FJLabs-Designs/FJ60BLX/Renders/v1-7-17-20-top.JPEG

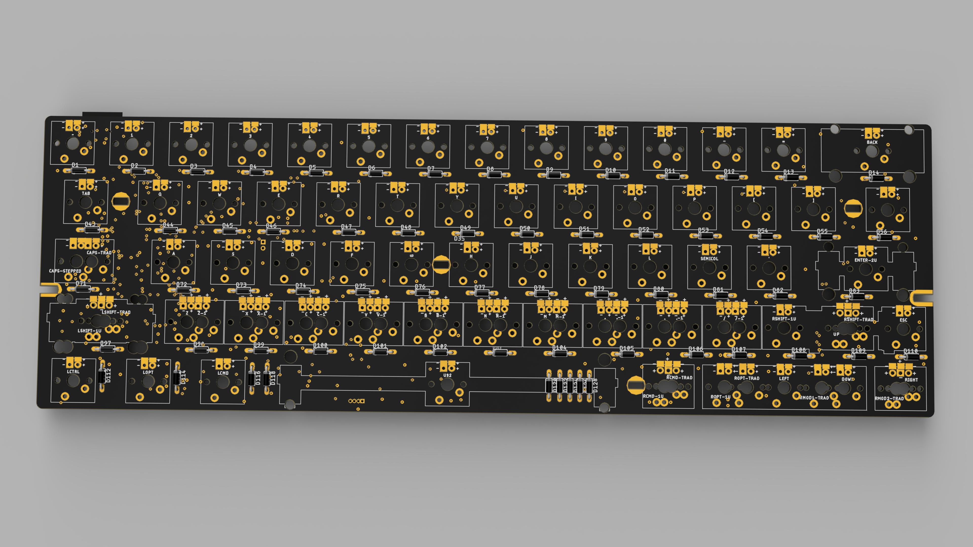
Renders/v1-7-17-20-top.JPEG
