FJLabs-Designs/FJ60BLX/Renders/v1-7-19-20-Bottom-2.jpg

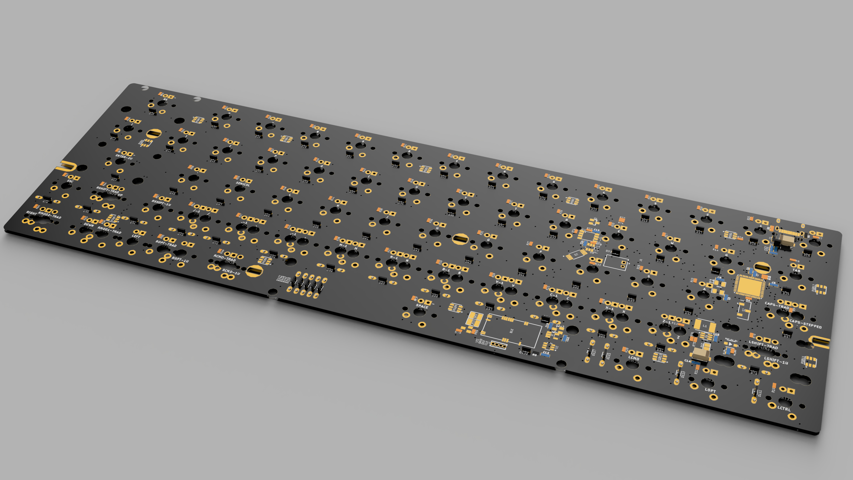
Renders/v1-7-19-20-Bottom-2.jpg
