FJLabs-Designs/FJ60BLX/Renders/v1-7-19-20-Top.jpg

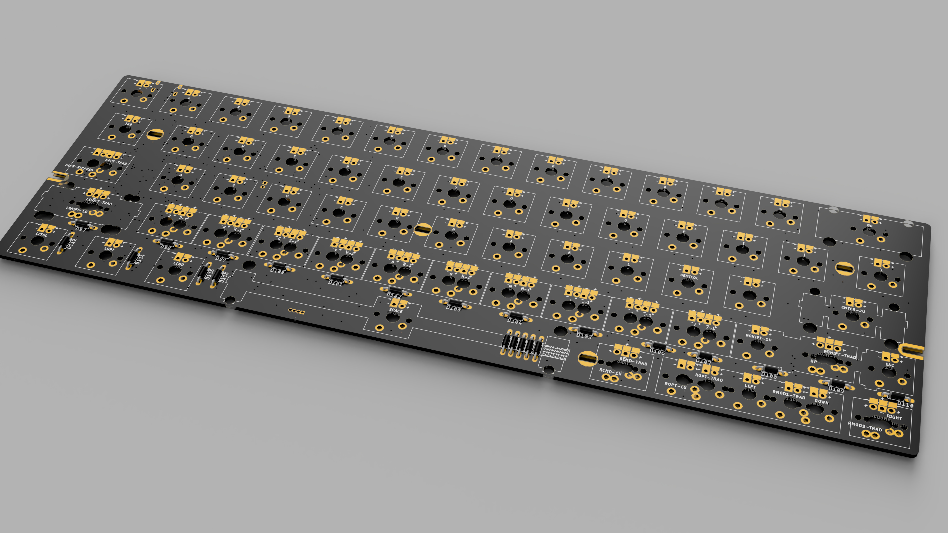
Renders/v1-7-19-20-Top.jpg
