FJLabs-Designs/FJ60BLX/Renders/v1-7-26-20-Split_Backspace.jpg

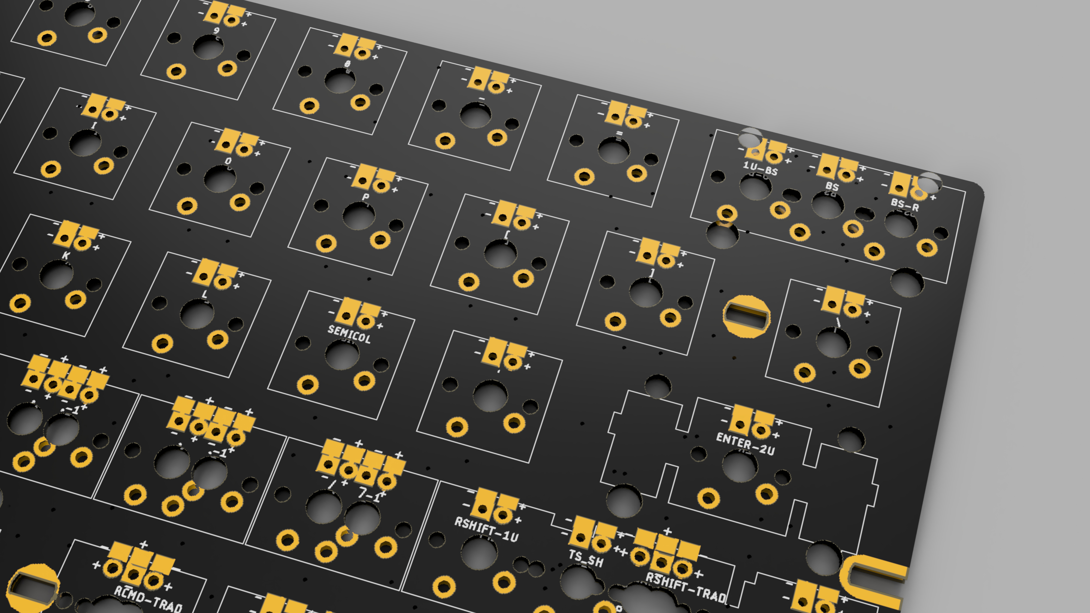
Renders/v1-7-26-20-Split_Backspace.jpg
