FJLabs-Designs/FJ60BLX/Renders/v1-7-26-20-TS_RShift.jpg

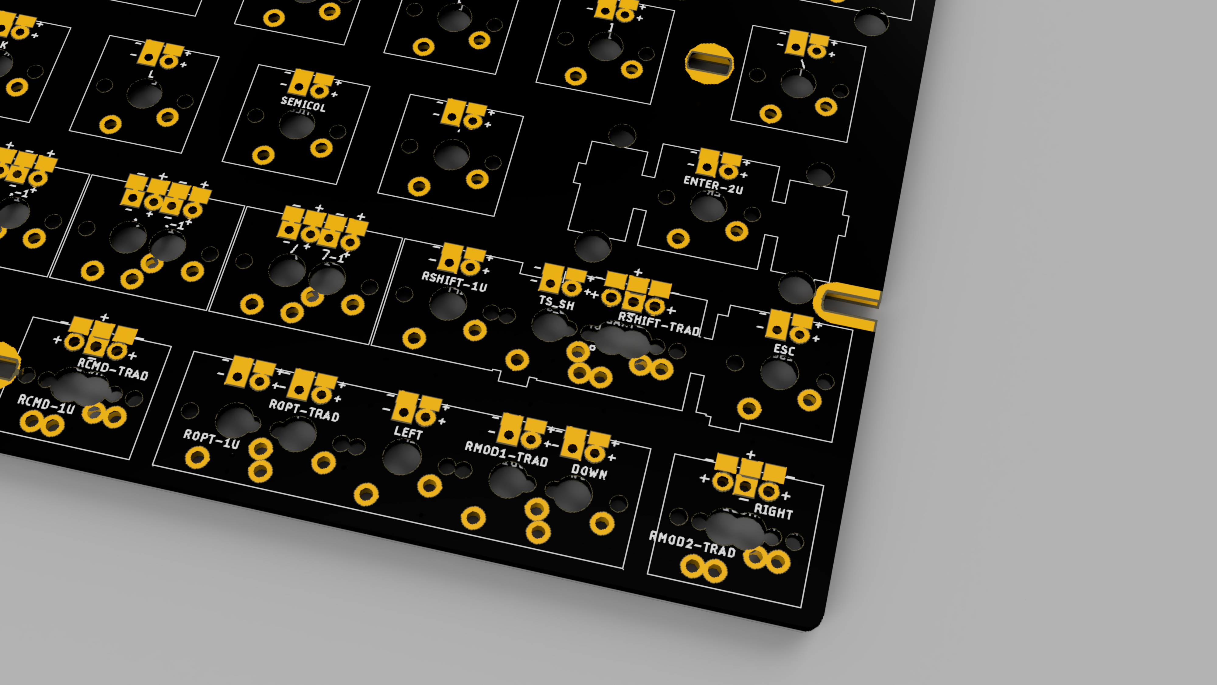
Renders/v1-7-26-20-TS_RShift.jpg
