FJLabs-Designs/FJ60BLX/Renders/v1-08-05-20-bottom.jpg

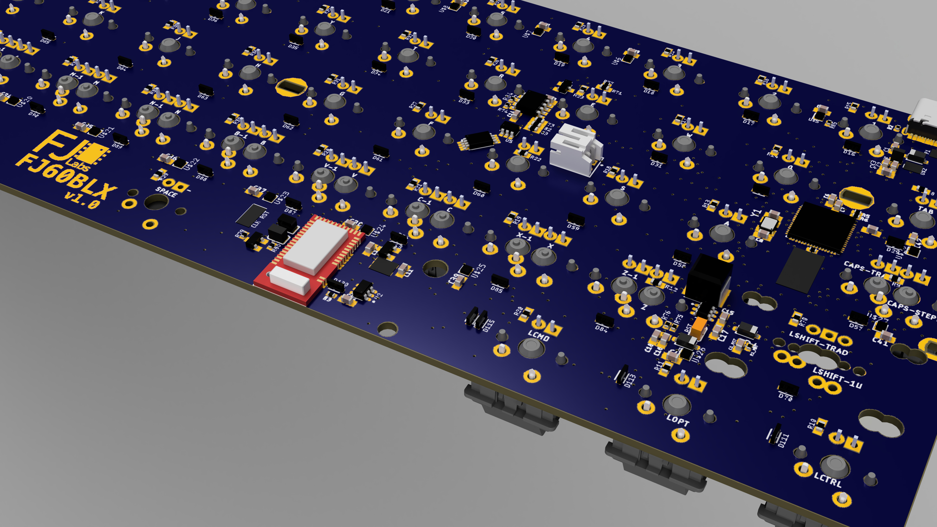
Renders/v1-08-05-20-bottom.jpg
