FJLabs-Designs/FJ60BLX/Renders/v1-8-20-20-whole.png

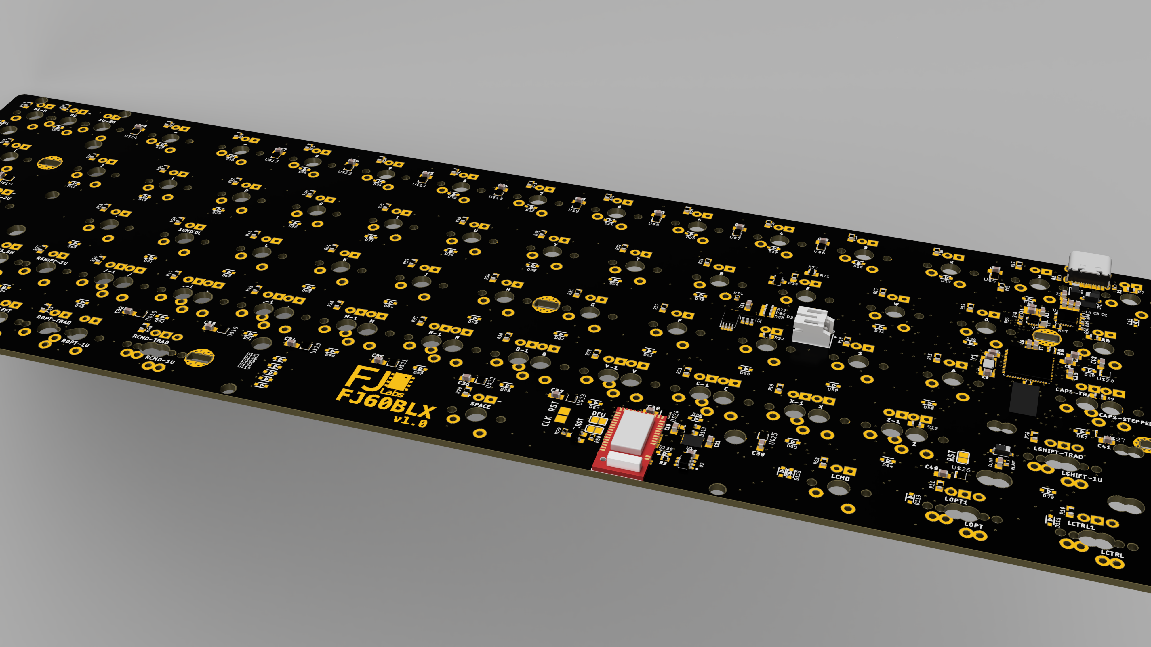
Renders/v1-8-20-20-whole.png
