FJLabs-Designs/FJ60BLX/Bill of Materials/GitHub BOM 9-4-2020.xlsx

Qty | Value | Device | Package | Parts | Description | Technology | Manufacturer Part # | LCSC Part # | LCSC Link
66 |  | DIODE-SOD323-R | SOD323-R | D1, D15, D16, D17, D18, D19, D20, D21, D22, D23, D24, D25, D26, D27, D28, D29, D30, D31, D32, D33, D34, D35, D36, D37, D38, D39, D40, D41, D42, D57, D58, D59, D60, D61, D62, D63, D64, D65, D66, D67, D68, D69, D70, D84, D85, D86, D87, D88, D89, D90, D91, D92, D93, D94, D95, D96, D111, D113, D115, D117, D119, D121, D123, D125, D127, D130 | 1N4148WS-7-F SMD Diode. SOD323-R Package [not flat leads] | SMD | 1N4148WS-7-F | C60580 | https://lcsc.com/product-detail/Switching-Diode_DIODES_1N4148WS-7-F_1N4148WS-7-F_C60580.html
2 | 100K | RESISTOR-0405 | R0402 | R86, R90 | 100K 0402 Resistor | SMD | RC-02W104JT | C280907 | https://lcsc.com/product-detail/Chip-Resistor-Surface-Mount_FH-Guangdong-Fenghua-Advanced-Tech-RC-02W104JT_C280907.html
28 | 100nF | CAPACITOR-0603 | C0603 | C1_RST, C4, C5, C14, C19, C20, C21, C22, C23, C24, C25, C26, C27, C28, C29, C30, C31, C32, C33, C34, C35, C36, C37, C38, C39, C40, C41, C42 | 100nF 0603 Capacitor | SMD | TCC0603X7R104K500CT | C282519 | https://lcsc.com/product-detail/Multilayer-Ceramic-Capacitors-MLCC-SMD-SMT_CCTC-TCC0603X7R104K500CT_C282519.html
7 | 10K | RESISTOR-0405 | R0402 | R1_RST, R3, R75, R77, R79, R80, R87 | 10K 0402 Resistor | SMD | RC-02W1002FT | C258091 | https://lcsc.com/product-detail/Chip-Resistor-Surface-Mount_FH-Guangdong-Fenghua-Advanced-Tech-RC-02W1002FT_C258091.html
9 | 10uF | CAPACITOR-0603 | C0603 | C1, C2, C11, C13, C15, C16, C43, C44, C45 | 10uF 0603 Capacitor | SMD | CL10A106MQ8NNNC | C1691 | https://lcsc.com/product-detail/Multilayer-Ceramic-Capacitors-MLCC-SMD-SMT_SAMSUNG_CL10A106MQ8NNNC_10uF-106-20-6-3V_C1691.html
1 | 120Ω @ 100MHz | BLM15HB221SN1 | 402 | L2 | 120Ohm @ 100MHz 600mA Ferrite Bead | SMD | FCM1005KF-121T06 | C304241 | https://lcsc.com/product-detail/Ferrite-Beads_TAITEC-FCM1005KF-121T06_C304241.html
2 | 12pF | CAPACITOR-0603 | C0603 | C8, C9 | 12pF 0603 Capacitor | SMD | 0603CG120J500NT | C1642 | https://lcsc.com/product-detail/Multilayer-Ceramic-Capacitors-MLCC-SMD-SMT_FH-Guangdong-Fenghua-Advanced-Tech-0603CG120J500NT_C1642.html
4 | 1K | RESISTOR-0405 | R0402 | R4, R74, R88, R89 | 1K 0402 Resistor | SMD | RC-02W1001FT | C226166 | https://lcsc.com/product-detail/Chip-Resistor-Surface-Mount_FH-Guangdong-Fenghua-Advanced-Tech-RC-02W1001FT_C226166.html
5 | 1uF | CAPACITOR-0603 | C0603 | C3, C6, C7, C10, C12 | 1uF 0603 Capacitor | SMD | 0603X105K160NT | C89188 | https://lcsc.com/product-detail/Multilayer-Ceramic-Capacitors-MLCC-SMD-SMT_FH-Guangdong-Fenghua-Advanced-Tech-0603X105K160NT_C89188.html
1 | 1uH | L_CHIP-0805(2012-METRIC) | INDC2009X120 | L3 | 1uH 0805 Inductor, >1A, <150mΩ ESR | SMD | CMH201209B1R0MT | C394956 | https://lcsc.com/product-detail/Power-Inductors_FH-Guangdong-Fenghua-Advanced-Tech-CMH201209B1R0MT_C394956.html
2 | 22 | RESISTOR-0405 | R0402 | R5, R6 | 22ohm 0402 Resistor [USB Data] | SMD | RC-02W22R0FT | C304591 | https://lcsc.com/product-detail/Chip-Resistor-Surface-Mount_FH-Guangdong-Fenghua-Advanced-Tech-RC-02W22R0FT_C304591.html
1 | 270K | RESISTOR-0405 | R0402 | R78 | 270K 0402 Resistor | SMD | RC-02W274JT | C321418 | https://lcsc.com/product-detail/Chip-Resistor-Surface-Mount_FH-Guangdong-Fenghua-Advanced-Tech-RC-02W274JT_C321418.html
70 | 300 | RESISTOR-0603 | R0603 | R7, R8, R9, R10, R11, R12, R13, R14, R15, R16, R17, R18, R19, R20, R21, R22, R23, R24, R25, R26, R27, R28, R29, R30, R31, R32, R33, R34, R35, R36, R37, R38, R39, R40, R41, R42, R43, R44, R45, R46, R47, R48, R49, R50, R51, R52, R53, R54, R55, R56, R57, R58, R59, R60, R61, R62, R63, R64, R65, R66, R67, R68, R69, R70, R71, R73, R81, R82, R83, R85 | 300ohm 0603 Resistor | SMD | RK73H1JTTD3000F | C139055 | https://lcsc.com/product-detail/Chip-Resistor-Surface-Mount_300R-300R-1_C139055.html
2 | 5.1K | RESISTOR-0405 | R0402 | R1, R2 | 5.1K 0402 Resistor | SMD | RTT025R10FTH | C103115 | https://lcsc.com/product-detail/Chip-Resistor-Surface-Mount_5-1R-5R10-1_C103115.html
1 | 7.2K | RESISTOR-0405 | R0402 | R72 | 7.5K 0402 Resistor | SMD | 0402WGF7501TCE | C25918 | https://lcsc.com/product-detail/Chip-Resistor-Surface-Mount_UNI-ROYAL-Uniroyal-Elec-0402WGF7501TCE_C25918.html
1 | 8MHz | CRYSTAL-4PIN-3.2X2.5 | CRYSTAL-3.2X2.5 | Y1 | 8MHz 10pF 4-Pad Crystal | SMD | TAXM8M4RDBCCT2T | C400090 | https://lcsc.com/product-detail/SMD-Crystal-Resonators_TAE-Zhejiang-Abel-Elec-TAXM8M4RDBCCT2T_C400090.html
1 | AT90USB646 | AT90USB1286-MU | QFN50P900X900X100-65N | U3 | AT90USB646 Microcontroller, QFN NoLeads Package | SMD | AT90USB646-MU | Microchip AT90USB646-MU: https://www.microchip.com/wwwproducts/en/AT90USB646
1 | BSS138 | BSS138 | SOT-23 | U$1 | BSS138 N Channel MOSFET for SWRST Level Shift | SMD | BSS138 | C427380 | https://lcsc.com/product-detail/MOSFET_MDD-Microdiode-Electronics-BSS138_C427380.html
1 | FDN337N | FDN337N | SSOT-3 | Q1 | N-Channel MOSFET | SMD | FDN337N | C475694 | https://lcsc.com/product-detail/New-Quadratic-Unclassified-Data_Shikues-FDN337N_C475694.html
1 | FS312F-G | FS312F-G | FS312F-G | U5 | Battery Protection IC FS312F-G | SMD | FS312F-G | C82736 | https://lcsc.com/product-detail/Battery-Protection-ICs_FS312F-G_C82736.html
1 | FS8205A | FS8205A | SOP65P640X120-8N | Q2 | Dual N-Channel MOSFET | SMD | FS8205A | C16052 | https://lcsc.com/product-detail/MOSFET_Fortune-Semicon-FS8205A_C16052.html
2 | MBR0520LT1G | CESD5V0D1 | SOD-123 | D3, D4 | 20V 500mA Schottky Diode | SMD | MBR0520LT1G | C23848 | https://lcsc.com/product-detail/Schottky-Barrier-Diodes-SBD_ON-Semiconductor-MBR0520LT1G_C23848.html
1 | MCP73871-2AAI/ML | MCP73871-2AAI/ML | QFN50P400X400X100-21N | U6 | MCP73871-2AAI/ML Battery Charging IC with Power Path Management | SMD | MCP73871-2AAI/ML | C144351 | https://lcsc.com/product-detail/PMIC-Battery-Management_Microchip-Tech-MCP73871-2AAI-ML_C144351.html
1 | MDBT40-NO-EXTRAMDBT40-NO-EXTRA | MDBT40-NO-EXTRAMDBT40-NO-EXTRA | MDBT40-NO-EXTRA | BLE | MDBT40 from Adafruit with Adafruit Firmware | SMD | MDBT40-256RV3 | Raytac MDBT40-256V3: https://www.raytac.com/product/ins.php?index_id=63
1 | MF-MSMF075-2 | CAPC1210X112N1210 | CAPC1210X112N | F1 | PTC Fuse for up to 1A 5V | SMD | MF-MSMF075-2 | C84140 | https://lcsc.com/product-detail/Surface-Mount-Fuses_BOURNS_MF-MSMF075-2_0-75A-13-2V-Self-healing-fuse_C84140.html
1 | MIC5205-3.3YM5TR | MIC5205-3.3YM5TR | SOT95P280X130-5N | U1 | Generic 3.3V Fixed Output LDO | SMD | ME6212C33M5G | C81233 | https://lcsc.com/product-detail/Dropout-Regulators-LDO_MICRONE-Nanjing-Micro-One-Elec-ME6212C33M5G_C81233.html
1 | PMEG2005CT | PMEG2005CT | SOT23 | D143 | Dual Schottky Barrier Diode, 20V.500mA | SMD | PMEG2005CT,215 | C282562 | https://lcsc.com/product-detail/Schottky-Barrier-Diodes-SBD_Nexperia-PMEG2005CT-215_C282562.html
1 | S2B-PH-K-S(LF)(SN) | S2B-PH-K-S(LF)(SN) | JST_S2B-PH-K-S(LF)(SN) | J1 | JST PH 2.0 [2 pin] Battery Connector, Right Angle, Through Hole | THT | S2B-PH-K-S(LF)(SN) | C173752 | https://lcsc.com/product-detail/Wire-To-Board-Wire-To-Wire-Connector_JST-Sales-America_S2B-PH-K-S-LF-SN_JST-Sales-America-S2B-PH-K-S-LF-SN_C173752.html
24 | SK6805 | SK6805 | SK6805 | U$5, U$6, U$7, U$8, U$9, U$10, U$11, U$12, U$13, U$14, U$15, U$16, U$17, U$18, U$19, U$20, U$21, U$22, U$23, U$24, U$25, U$26, U$27, U$28 | SK6805 equivalent Addressable RGB LED's | SMD | DY-S1515065/RGBC/6805-5T | C524053 | https://lcsc.com/product-detail/Light-Emitting-Diodes-LED_TONYU-DY-S1515065-RGBC-6805-5T_C524053.html
1 | SN74LVC2G34DBVR | SN74LVC2G34DBVR | SOT95P280X145-6N | U2 | 5V to 3.3V Level Shifter Dual Channel | THT | SN74LVC2G34DBVR | C347589 | https://lcsc.com/product-detail/Logic-Buffers-Drivers-Receivers-Transceivers_Texas-Instruments_SN74LVC2G34DBVR_Texas-Instruments-Texas-Instruments-SN74LVC2G34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
1 | SSSS213000 | SSSS213000 | SSSS213000 | S2 | Switch Slide Spdt 300ma 6v | SMD | SSSS213000 | C125054 | https://lcsc.com/product-detail/Toggle-Switches_ALPS-Electric-SSSS213000_C125054.html
1 | TPS61252DSGT | TPS61252DSGT | SON50P200X200X80-9N | U7 | TPS61252DSGR/T Boost Converter IC | SMD | TPS61252DSGR | C128617 | https://lcsc.com/product-detail/DC-DC-Converters_Texas-Instruments_TPS61252DSGR_Texas-Instruments-Texas-Instruments-TPS61252DSGR_C128617.html
1 | USB-C | USB-C | TYPE-C-31-M-12 | USB-C | USB C Port | SMD/THT | TYPE-C-31-M-12 | C165948 | https://lcsc.com/product-detail/USB-Type-C_Korean-Hroparts-Elec-TYPE-C-31-M-12_C165948.html
1 | USBLC6-2P6 | USBLC6-2P6 | SOT50P160X60-6N | U4 | USB ESD Protection Diode with Powerline Protection | SMD | USBLC6-2P6 | C15999 | https://lcsc.com/product-detail/Diodes-ESD_STMicroelectronics_USBLC6-2P6_USBLC6-2P6_C15999.html
64 | LED-0805 | LED-0805 | LED0805 | U$29, U$30, U$31, U$32, U$33, U$34, U$35, U$36, U$37, U$38, U$39, U$40, U$41, U$42, U$43, U$44, U$45, U$46, U$47, U$48, U$49, U$50, U$51, U$52, U$53, U$54, U$55, U$56, U$57, U$58, U$59, U$60, U$61, U$62, U$63, U$64, U$65, U$66, U$67, U$68, U$69, U$70, U$71, U$72, U$73, U$74, U$75, U$76, U$77, U$78, U$79, U$80, U$81, U$82, U$83, U$84, U$85, U$86, U$87, U$88, U$89, U$90, U$91, U$92 | White 0805 SMD LED | SMD | ORH-W45A | C205447 | https://lcsc.com/product-detail/Light-Emitting-Diodes-LED_0805-white_C205447.html | ASSEMBLE ON ONLY ONE BOARD
