FJLabs-Designs/FJ60BLX/Component Analysis/images/atmega32u4-qfp.jpeg

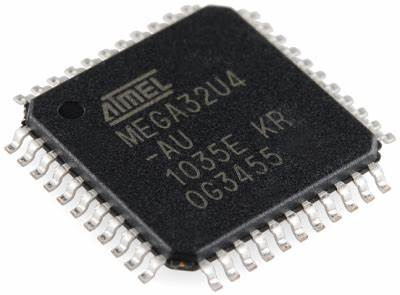
Component Analysis/images/atmega32u4-qfp.jpeg
